Scottz0r/fisher-price-keypad/arduino/fp_keypad_itsy_bitsy/color_tables.h

#ifndef _SCOTTZ0R_COLOR_TABLES_INCLUDE_GUARD
#define _SCOTTZ0R_COLOR_TABLES_INCLUDE_GUARD

#include "avr/pgmspace.h"
#include "hw_led.h"

namespace colors
{
    using scottz0r::color_t;

    const color_t red_lut[] PROGMEM = {
        5, 0, 0,
        10, 0, 0,
        15, 0, 0,
        20, 0, 0,
        26, 0, 0,
        31, 0, 0,
        36, 0, 0,
        41, 0, 0,
        46, 0, 0,
        51, 0, 0,
        56, 0, 0,
        61, 0, 0,
        66, 0, 0,
        71, 0, 0,
        76, 0, 0,
        82, 0, 0,
        87, 0, 0,
        92, 0, 0,
        97, 0, 0,
        102, 0, 0,
        107, 0, 0,
        112, 0, 0,
        117, 0, 0,
        122, 0, 0,
        128, 0, 0,
        133, 0, 0,
        138, 0, 0,
        143, 0, 0,
        148, 0, 0,
        153, 0, 0,
        158, 0, 0,
        163, 0, 0,
        168, 0, 0,
        173, 0, 0,
        178, 0, 0,
        184, 0, 0,
        189, 0, 0,
        194, 0, 0,
        199, 0, 0,
        204, 0, 0,
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
    };

    const color_t green_lut[] PROGMEM = {
        0, 5, 0,
        0, 10, 0,
        0, 15, 0,
        0, 20, 0,
        0, 26, 0,
        0, 31, 0,
        0, 36, 0,
        0, 41, 0,
        0, 46, 0,
        0, 51, 0,
        0, 56, 0,
        0, 61, 0,
        0, 66, 0,
        0, 71, 0,
        0, 76, 0,
        0, 82, 0,
        0, 87, 0,
        0, 92, 0,
        0, 97, 0,
        0, 102, 0,
        0, 107, 0,
        0, 112, 0,
        0, 117, 0,
        0, 122, 0,
        0, 128, 0,
        0, 133, 0,
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
        138, 9, 0,
        143, 10, 0,
        148, 10, 0,
        153, 10, 0,
        158, 11, 0,
        163, 11, 0,
        168, 11, 0,
        173, 12, 0,
        178, 12, 0,
        184, 12, 0,
        189, 13, 0,
        194, 13, 0,
        199, 13, 0,
        204, 14, 0,
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
    };

}
#endif
