Scottz0r/fisher-price-keypad/arduino/fp_keypad_itsy_bitsy/color_mapper.h

#ifndef _SCOTTZOR_COLOR_MANAGER_H_INCLUDE_GUARD
#define _SCOTTZOR_COLOR_MANAGER_H_INCLUDE_GUARD

#include "look_up_table.h"

namespace scottz0r {

    const LookUpTable* map_key_to_color(char key_char);
}

#endif // _SCOTTZOR_COLOR_MANAGER_H_INCLUDE_GUARD
