Scottz0r/fisher-price-keypad/arduino/fp_keypad_itsy_bitsy/globals.h

#ifndef _SCOTTZ0R_GLOBALS_H_INCLUDE_GUARD
#define _SCOTTZ0R_GLOBALS_H_INCLUDE_GUARD

#include "keypad.h"
#include "led_manager.h"

namespace scottz0r
{
    // Declare in ino
    extern Keypad keypad;
    extern LedManager led_manager;
}

#endif // _SCOTTZ0R_GLOBALS_H_INCLUDE_GUARD
