Scottz0r/fisher-price-keypad/arduino/fp_keypad_itsy_bitsy/color_manager.h

#ifndef _SCOTTZOR_COLOR_MANAGER_H_INCLUDE_GUARD
#define _SCOTTZOR_COLOR_MANAGER_H_INCLUDE_GUARD

namespace scottz0r { namespace colorman {

    void begin();

    void play(int key_code);

}}

#endif // _SCOTTZOR_COLOR_MANAGER_H_INCLUDE_GUARD
