Scottz0r/fisher-price-keypad/arduino/fp_keypad_itsy_bitsy/prj_generic_types.h

#ifndef _SCOTTZ0R_PRJ_GENERIC_TYPES_INCLUE_GUARD
#define _SCOTTZ0R_PRJ_GENERIC_TYPES_INCLUE_GUARD

#define scottz0r_array_size(a) (sizeof(a)/sizeof(a[0]))

namespace scottz0r
{
    using size_type = unsigned int;

    using time_type = unsigned long;
}

#endif // _SCOTTZ0R_PRJ_GENERIC_TYPES_INCLUE_GUARD
